samo4/CPDEL/firmware/esp/main/wireless_controller.h

#pragma once

#include <stdbool.h>
#include <stddef.h>
#include "esp_err.h"

void wireless_init(void);
void wireless_pause(void);
esp_err_t wireless_save_credentials(const char *ssid, const char *password, bool reboot);
esp_err_t wireless_get_ssid(char *ssid, size_t ssid_size);
