samo4/CPDEL/firmware/sim/lv_drv_conf.h

#ifndef LV_DRV_CONF_H
#define LV_DRV_CONF_H
#include "lv_conf.h"

#define USE_SDL 1
#define SDL_HOR_RES 320
#define SDL_VER_RES 240
#define SDL_ZOOM 2
#define SDL_DOUBLE_BUFFER 0
#define SDL_DUAL_DISPLAY 0
// #define USE_MOUSE 1
// #define USE_MOUSEWHEEL 1
// #define USE_KEYBOARD 1

#ifndef SDL_INCLUDE_PATH
#define SDL_INCLUDE_PATH <SDL2/SDL.h>
#endif

#endif /*LV_DRV_CONF_H*/
